sparkfun/SparkFun_Artemis_Global_Tracker/img/16469-Artemis_Global_Tracker-02.jpg

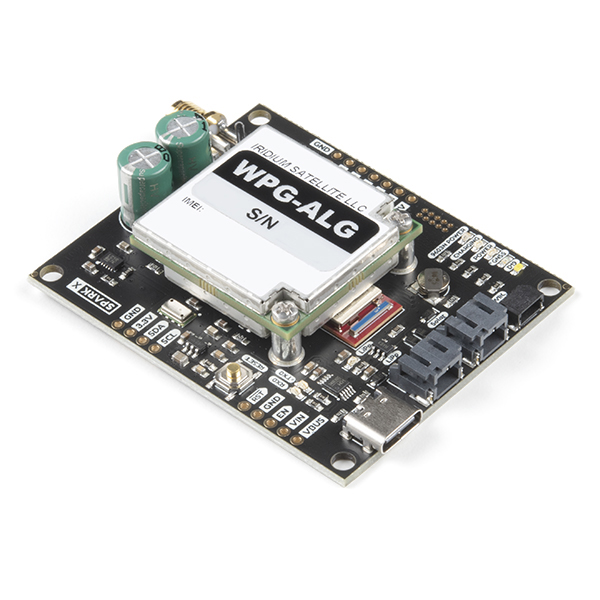
img/16469-Artemis_Global_Tracker-02.jpg
