sparkfun/SparkFun_Artemis_Global_Tracker/img/16469-Artemis_Global_Tracker-04.jpg

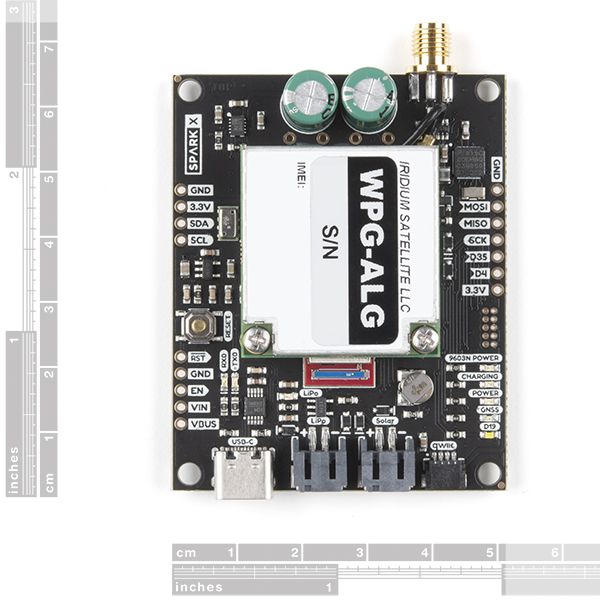
img/16469-Artemis_Global_Tracker-04.jpg
