sparkfun/SparkFun_Artemis_Global_Tracker/img/Bottom.JPG

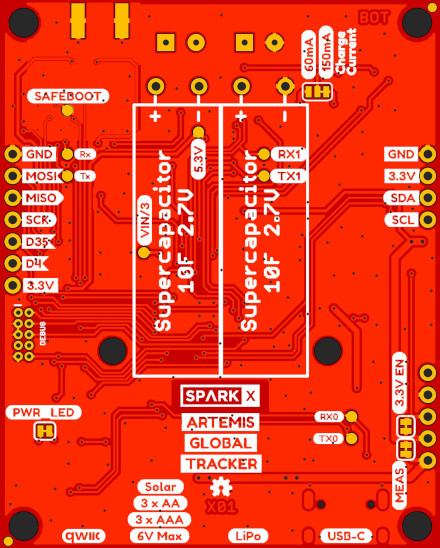
img/Bottom.JPG
