sparkfun/SparkFun_Artemis_Global_Tracker/img/Config.JPG

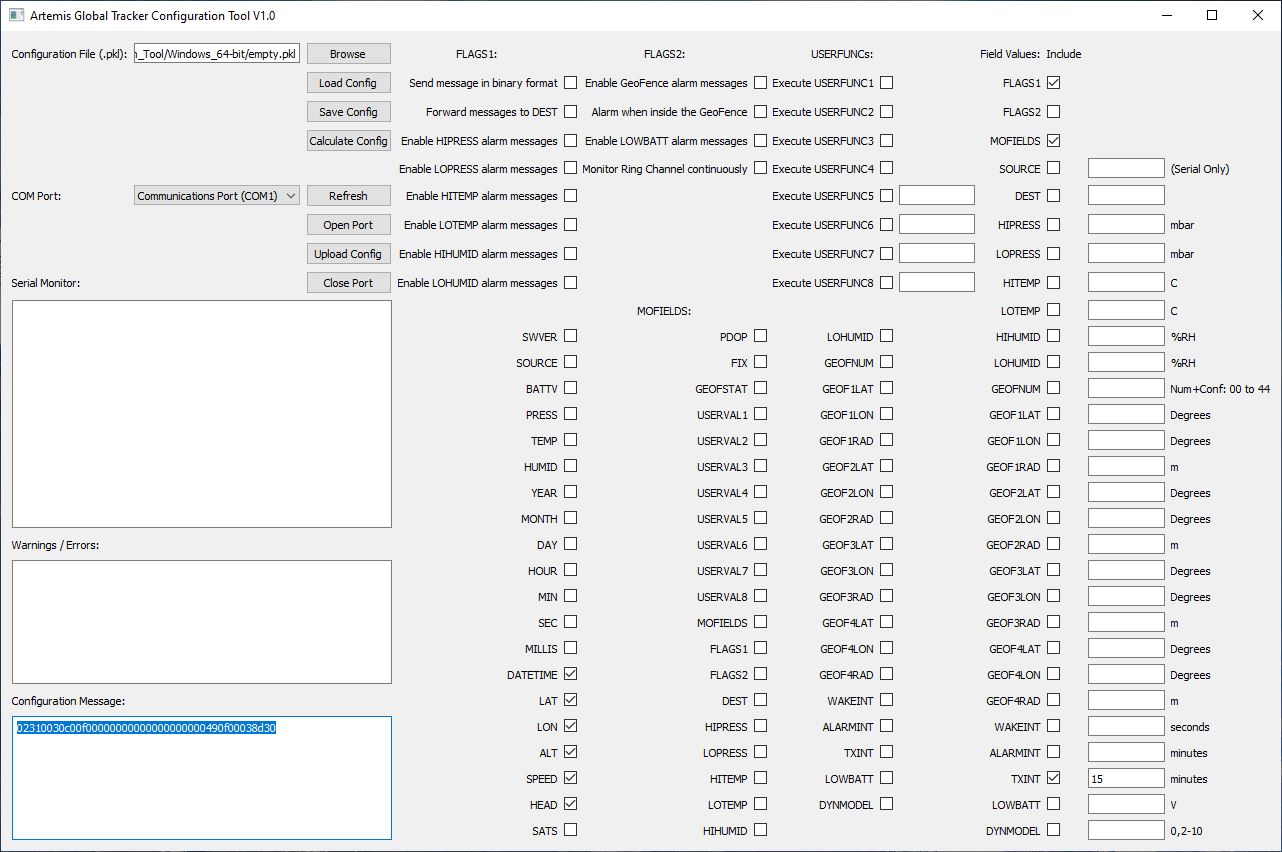
img/Config.JPG
