sparkfun/SparkFun_Artemis_Global_Tracker/img/Delivery_Group.PNG

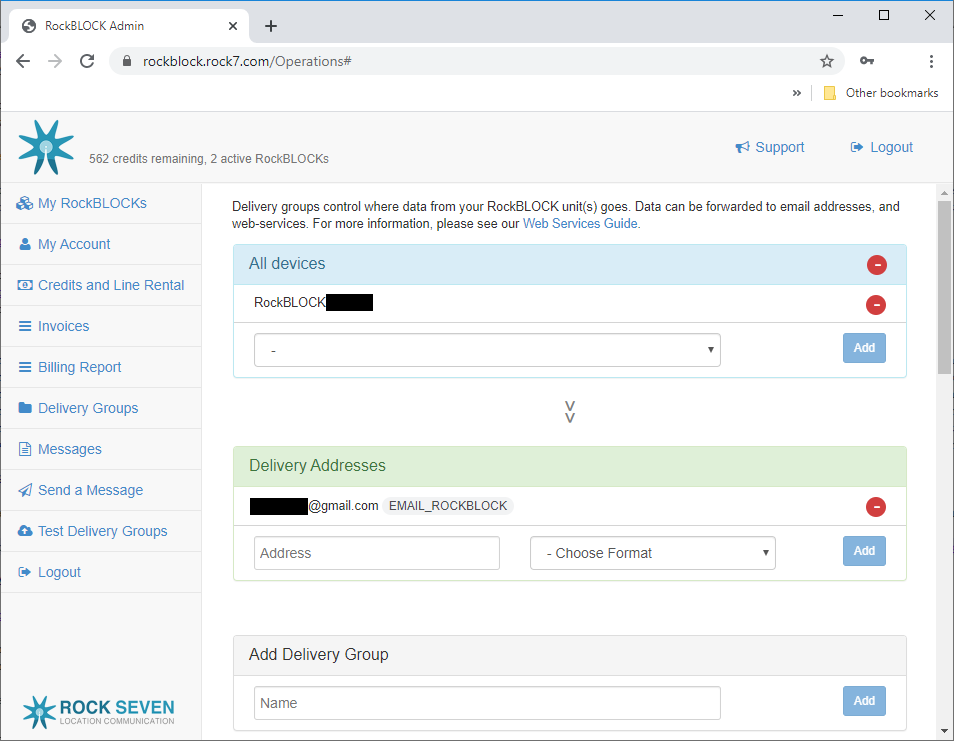
img/Delivery_Group.PNG
