sparkfun/SparkFun_Artemis_Global_Tracker/img/Google_Earth.JPG

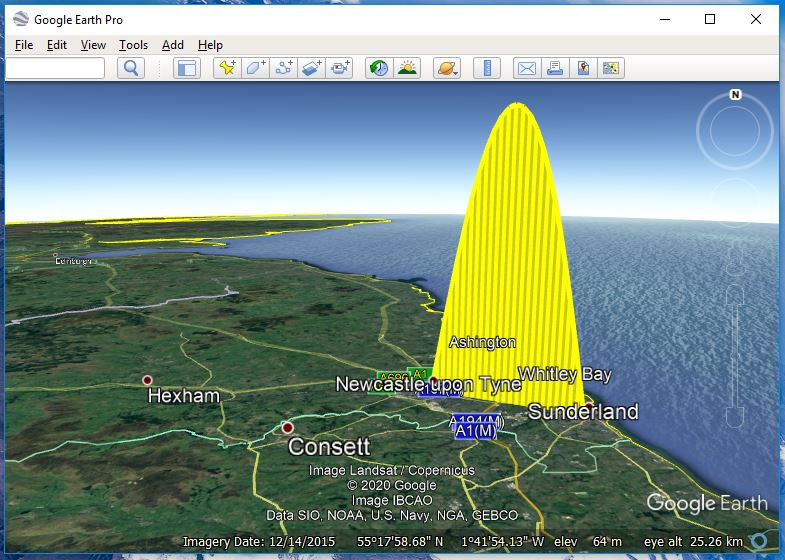
img/Google_Earth.JPG
