sparkfun/SparkFun_Artemis_Global_Tracker/img/Mapper.JPG

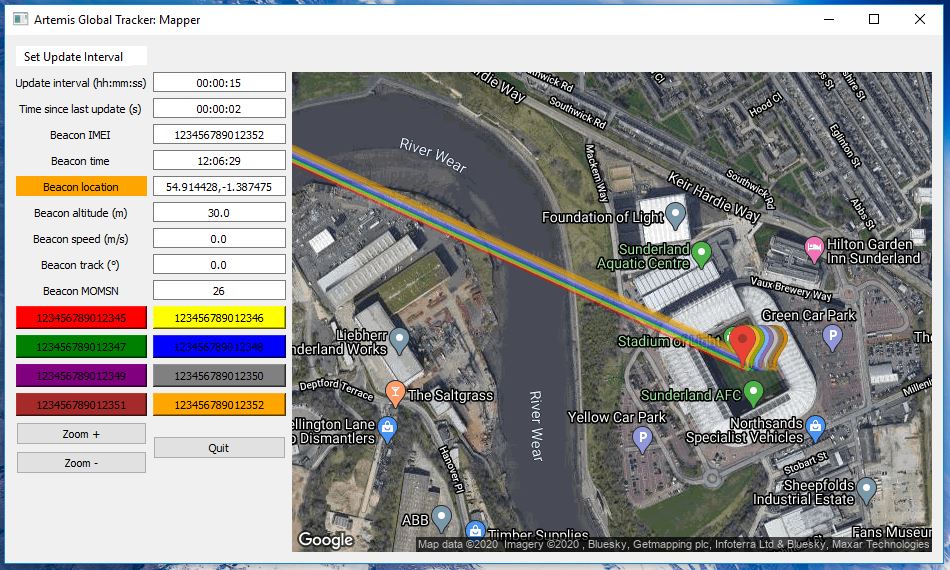
img/Mapper.JPG
