sparkfun/SparkFun_Artemis_Global_Tracker/img/Quickstart2.PNG

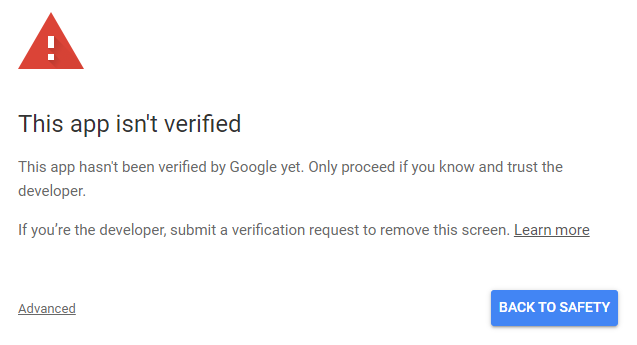
img/Quickstart2.PNG
