sparkfun/SparkFun_Artemis_Global_Tracker/img/Quickstart4.PNG

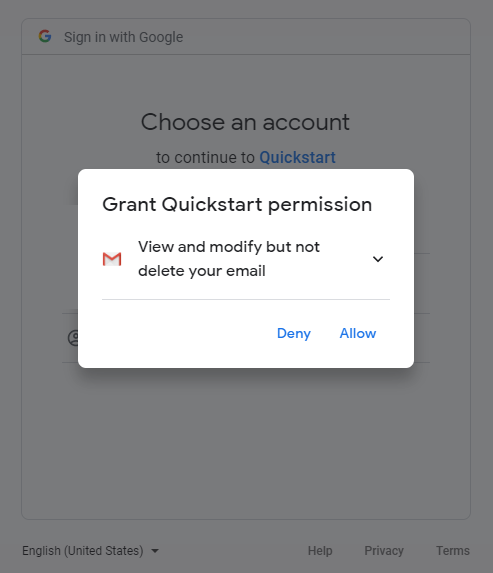
img/Quickstart4.PNG
