sparkfun/SparkFun_Artemis_Global_Tracker/img/Quickstart5.PNG

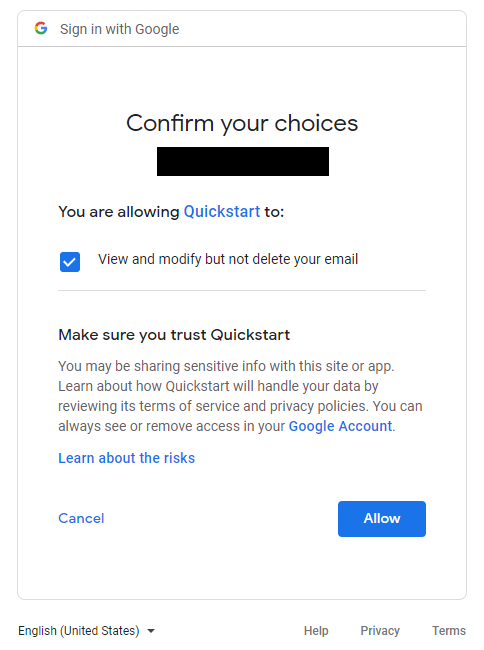
img/Quickstart5.PNG
