sparkfun/SparkFun_Artemis_Global_Tracker/img/Tracker_with_Internet.JPG

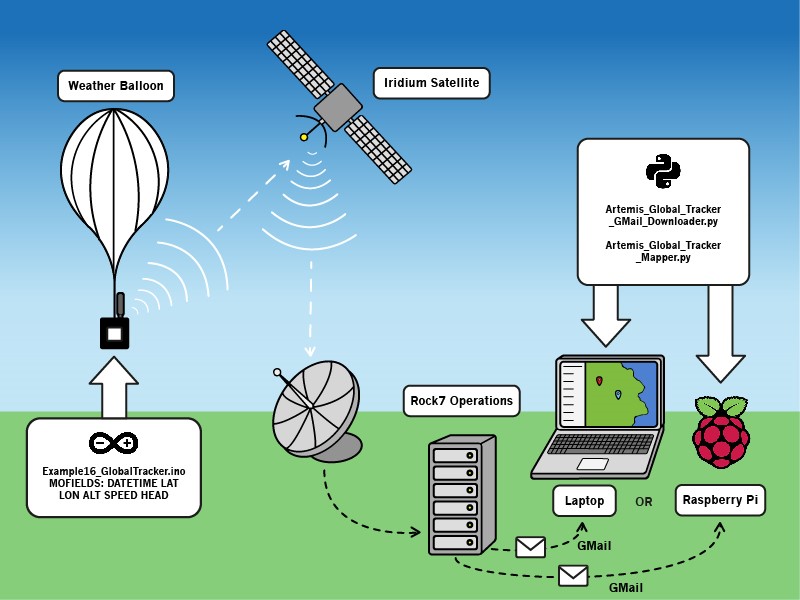
img/Tracker_with_Internet.JPG
