sparkfun/SparkFun_Artemis_Global_Tracker/img/ZOE-M8Q_Paste.JPG

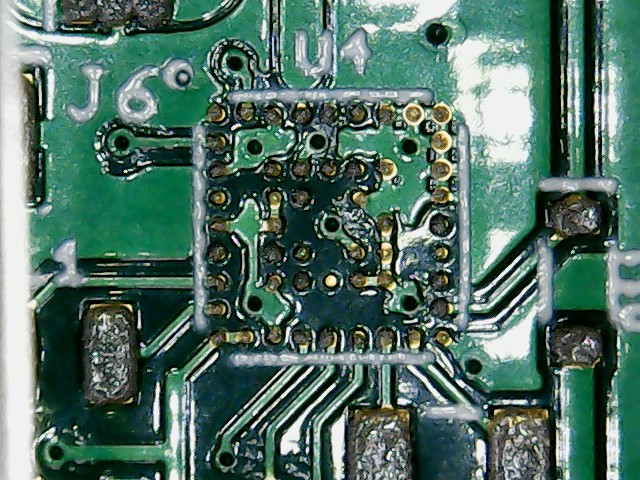
img/ZOE-M8Q_Paste.JPG
