sparkfun/SparkFun_Artemis_Global_Tracker/Tools/Artemis_Global_Tracker_Mapping_Tools/map_image_blank.png

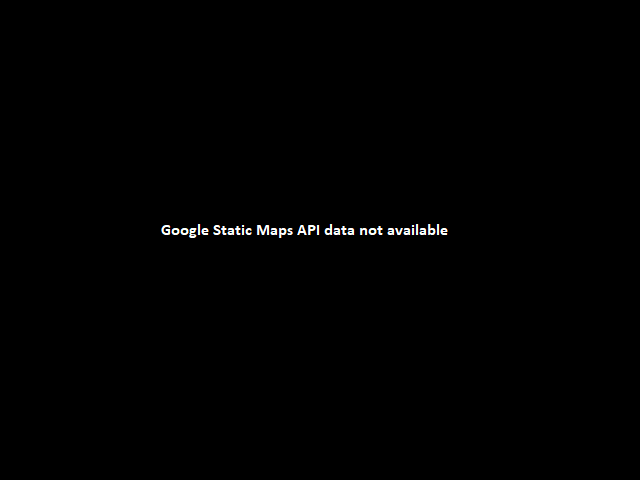
Tools/Artemis_Global_Tracker_Mapping_Tools/map_image_blank.png
